deltaphi/RR32CanController/src/application/controller/MasterControl.cpp

#include <application/controller/MasterControl.h>
#include <cstring>

#include "RR32Can/RR32Can.h"

namespace application {
namespace controller {

void MasterControl::begin(application::controller::SettingsStorageCbk& settingsCbk,
                          application::controller::TurnoutMapStorageCbk& turnoutMapStorageCallback,
                          application::controller::ActionlistStorageCbk& actionListCallback) {
  systemState = RR32Can::SystemState::UNKNOWN;

  inputState.reset();

  displayModel.begin();
  enterIdle();

  locoControl.begin();
  locoList.begin();

  turnoutControl.begin(actionListCallback, turnoutMapStorageCallback);

  settingsMenu.begin(settingsCbk);
  turnoutMenu.begin(turnoutMapStorageCallback);
}

void MasterControl::loop() {
  // Always evaluate the STOP key with no SHIFT support
  loopStopKey();

  checkStateTransition();
  forwardLoop();

  updateDisplayLoop();

  turnoutControl.loop(inputState);
}

void MasterControl::checkStateTransition() {
  switch (uiMode) {
    case UIMode::IDLE:
    case UIMode::LOCOCONTROL:
    case UIMode::LOCOLIST:
    case UIMode::SETTINGS:
    case UIMode::TURNOUTMAPPING:
      break;
    case UIMode::LOCODOWNLOAD:
      // Switch to control when an engine was downloaded.
      if (locoControl.hasValidEngine()) {
        enterLocoControl();
      }
  }
}

void MasterControl::forwardLoop() {
  // Depending on mode, loop the associated control
  switch (uiMode) {
    case UIMode::IDLE:
      idleControl.loop(inputState, *this);
      break;
    case UIMode::LOCOCONTROL:
    case UIMode::LOCODOWNLOAD:
      locoControl.loop(inputState, *this);
      break;
    case UIMode::LOCOLIST:
      locoList.loop(inputState, *this);
      break;
    case UIMode::SETTINGS:
      settingsMenu.loop(inputState, *this);
      break;
    case UIMode::TURNOUTMAPPING:
      turnoutMenu.loop(inputState, *this, turnoutControl.getTurnoutMap(),
                       turnoutControl.getActionListModel().getDb());
  }
}

void MasterControl::enterIdle() {
  printf("MasterControl::enterIdle\n");
  uiMode = UIMode::IDLE;
  idleControl.updateDisplayOnce(displayModel);
}

void MasterControl::enterLocoControl() {
  printf("MasterControl::enterLocoControl\n");
  if (!locoControl.hasValidEngine()) {
    enterIdle();
  } else {
    displayModel.disableCursor();
    uiMode = UIMode::LOCOCONTROL;
    locoControl.enterLocoControl(inputState);
    locoControl.requestLocoData();
    locoControl.updateDisplayOnce(displayModel);
  }
}

void MasterControl::enterLocoList() {
  printf("MasterControl::enterLocoList\n");
  uiMode = UIMode::LOCOLIST;
  inputState.loadEncoderPosition(locoList.getCurrentItem());
  locoList.RequestDownloadAtCursor();
  displayModel.disableCursor();
  locoList.forceDisplayUpdate();
}

void MasterControl::enterLocoDownload() {
  printf("MasterControl::enterLocoDownload\n");
  uiMode = UIMode::LOCODOWNLOAD;

  // Copy selected engine from locoList to locoControl and start the download of
  // data
  const RR32Can::LocomotiveShortInfo* locoInfo = locoList.getSelectedEngine();
  if (locoInfo == nullptr) {
    // No engine was selected, go to IDLE
    enterIdle();
  } else {
    if (!locoControl.setLocoInfo(*locoInfo)) {
      // Previous Engine was reselected, go to another mode
      if (locoControl.hasValidEngine()) {
        enterLocoControl();
      } else {
        enterIdle();
      }
    } else {
      // An actual change was made. Update the UI.
      locoControl.updateDisplayOnce(displayModel);

      // Request the "lokomotive" data.
      locoControl.requestLocoFile();
    }
  }
}

void MasterControl::enterSettingsMenu() {
  printf("MasterControl::enterSettingsMenu\n");
  uiMode = UIMode::SETTINGS;
  inputState.loadEncoderPosition(settingsMenu.getCurrentItem());
  settingsMenu.forceDisplayUpdate();
}

void MasterControl::enterTurnoutMenu() {
  printf("MasterControl::enterTurnoutMenu\n");
  uiMode = UIMode::TURNOUTMAPPING;
  displayModel.disableCursor();
  turnoutMenu.forceDisplayUpdate();
}

void MasterControl::updateDisplayLoop() {
  switch (uiMode) {
    case UIMode::IDLE:
      // Was set during entering, nothing to do.
      break;
    case UIMode::LOCOLIST:
      // Handled by LOCOLIST itself
      locoList.updateDisplay(displayModel);
      break;
    case UIMode::LOCODOWNLOAD:
    case UIMode::LOCOCONTROL:
      break;
    case UIMode::SETTINGS:
      settingsMenu.updateDisplay(displayModel);
      break;
    case UIMode::TURNOUTMAPPING:
      turnoutMenu.updateDisplay(displayModel, turnoutControl.getTurnoutMap());
  }

  // Always update the non-text loco artifacts
  locoControl.updateDisplayLoop(displayModel);
}

void MasterControl::loopStopKey() {
  // Read the STOP button
  if (inputState.isStopRisingEdge()) {
    if (displayModel.getSystemOn()) {
      RR32Can::RR32Can.SendSystemStop();
    } else {
      RR32Can::RR32Can.SendSystemGo();
    }
  }
}

RR32Can::Locomotive* MasterControl::getLoco(RR32Can::Locomotive::Uid_t engineUid) {
  RR32Can::Locomotive& loco = locoControl.getLoco();
  if (!loco.isFullDetailsKnown()) {
    return nullptr;
  }
  if (loco.getUidMasked() != engineUid) {
    return nullptr;
  }

  return &loco;
}

void MasterControl::setLocoVelocity(RR32Can::Locomotive::Uid_t uid, RR32Can::Velocity_t velocity) {
  if (getLoco(uid) != 0) {
    locoControl.setReceivedVelocity(velocity, *this);
  }
}

void MasterControl::setLocoVelocity(RR32Can::Velocity_t velocity) {
  locoControl.setReceivedVelocity(velocity, *this);
}

}  // namespace controller
}  // namespace application
