deltaphi/RR32CanController/src/application/controller/LocoList.h

#ifndef __APPLICATION__CONTROLLER__LOCOLIST_H__
#define __APPLICATION__CONTROLLER__LOCOLIST_H__

#include <RR32Can/LocoListConsumer.h>
#include <RR32Can/Locomotive.h>
#include "application/controller/AbstractMenu.h"
#include "application/model/DisplayModel.h"
#include "application/model/InputState.h"

namespace application {
namespace controller {

class MasterControl;

/*
 * \brief Class LocoList
 */
class LocoList : public application::controller::AbstractMenu {
 public:
  void begin();
  void loop(application::model::InputState& inputState, MasterControl& masterControl) override;

  /// Callback when a menu item is selected.
  void advanceMenu(MenuItemIndex_t menuItem, MasterControl& masterControl) override;

  /// Callback when the menu is aborted (shift+encoder)
  void abortMenu(MasterControl& masterControl) override;

  const RR32Can::LocomotiveShortInfo* getSelectedEngine();

  void getMenuItems(MenuItems_t& menuItems) override;

  void notifyEncoderMoved(MenuItemIndex_t newItem) override;

  MenuItemIndex_t getTotalMenuLength() override { return browser.getNumEnginesKnownByMaster(); }

  void RequestDownloadAtCursor();

 private:
  RR32Can::LocoListConsumer browser;
};

}  // namespace controller
}  // namespace application

#endif  // __APPLICATION__CONTROLLER__LOCOLIST_H__
