deltaphi/RR32CanController/src/application/controller/SettingsMenu.h

#ifndef __APPLICATION__CONTROLLER__SETTINGSMENU_H__
#define __APPLICATION__CONTROLLER__SETTINGSMENU_H__

#include "application/controller/AbstractMenu.h"
#include "application/controller/SettingsStorageCbk.h"
#include "application/model/InputState.h"
#include "application/model/Settings.h"

namespace application {
namespace controller {

class MasterControl;

/*
 * \brief Class SettingsMenu
 */
class SettingsMenu : public application::controller::AbstractMenu {
 public:
  static constexpr const uint8_t kNumMenuEntries = 3;

  void begin(application::controller::SettingsStorageCbk& storageCbk);

  const application::model::Settings& getUserSettings() const { return settings; }

 protected:
  /// Callback when a menu item is selected.
  void advanceMenu(MenuItemIndex_t menuItem, MasterControl& masterControl) override;

  /// Callback when the menu is aborted (shift+encoder)
  void abortMenu(MasterControl& masterControl) override;

  /**
   * \brief Callback to retrive an array of menuitems.
   *
   * This is called fairly frequently, thus it should be implemented
   * efficiently.
   */
  void getMenuItems(MenuItems_t& menuItems) override;

  /**
   * \brief Callback to obtian the current known length of the menu.
   *
   * The length is not assumed to be constant for a given menu.
   */
  MenuItemIndex_t getTotalMenuLength() override;

 private:
  static const char* kTurnoutMapping;
  static const char* kUseCAN;
  static const char* kUseWifi;
  static const char* kActionListMapping;
  static const char* kWifiSettingsMapping;
  static const char* kConnectionSettingsMapping;

  static const char* kMenuEntries[kNumMenuEntries];

  application::model::Settings settings;
  application::controller::SettingsStorageCbk* storageCbk = nullptr;
};

}  // namespace controller
}  // namespace application

#endif  // __APPLICATION__CONTROLLER__SETTINGSMENU_H__
