deltaphi/RR32CanController/src/hal/UIAssets.h

#ifndef __HAL__UIASSETS_H__
#define __HAL__UIASSETS_H__

#include <Arduino.h>

namespace hal {

enum class RR32SymbolNames : char {
  ARROW_LEFT_EMPTY = 1,
  ARROW_LEFT_FILLED = 2,
  ARROW_RIGHT_EMPTY = 3,
  ARROW_RIGHT_FILLED = 4,
  WIFI = 5
};

// Font generated or edited with the glyphEditor
constexpr const uint8_t RR32Symbols_8[] PROGMEM = {
    0x08,  // Width: 8
    0x08,  // Height: 8
    0x01,  // First char: 1
    0x05,  // Number of chars: 5
    // Jump Table:
    0x00, 0x00, 0x08, 0x08,  // 1
    0x00, 0x08, 0x08, 0x08,  // 2
    0x00, 0x10, 0x07, 0x08,  // 3
    0x00, 0x17, 0x07, 0x08,  // 4
    0x00, 0x1E, 0x08, 0x08,  // 5
    // Font Data:
    0x00, 0x18, 0x24, 0x42, 0xE7, 0x24, 0x24, 0x3C,  // 1
    0x00, 0x18, 0x3C, 0x7E, 0xFF, 0x3C, 0x3C, 0x3C,  // 2
    0x3C, 0x24, 0x24, 0xE7, 0x42, 0x24, 0x18,        // 3
    0x3C, 0x3C, 0x3C, 0xFF, 0x7E, 0x3C, 0x18,        // 4
    0x0A, 0x25, 0x15, 0xD5, 0xD5, 0x15, 0x25, 0x0A,  // 5
};

// Font generated or edited with the glyphEditor
constexpr const uint8_t RR32Symbols_10[] PROGMEM = {
    0x0A,  // Width: 10
    0x0A,  // Height: 10
    0x01,  // First char: 1
    0x05,  // Number of chars: 5
    // Jump Table:
    0x00, 0x00, 0x13, 0x0A,  // 1
    0x00, 0x13, 0x13, 0x0A,  // 2
    0x00, 0x26, 0x13, 0x0A,  // 3
    0x00, 0x39, 0x13, 0x0A,  // 4
    0x00, 0x4C, 0x13, 0x0A,  // 5
    // Font Data:
    0x30, 0x00, 0x48, 0x00, 0x84, 0x00, 0x02, 0x01, 0x01, 0x02, 0x87, 0x03, 0x84, 0x00, 0x84, 0x00,
    0x84, 0x00, 0xFC,  // 1
    0x30, 0x00, 0x78, 0x00, 0xFC, 0x00, 0xFE, 0x01, 0xFF, 0x03, 0xFF, 0x03, 0xFC, 0x00, 0xFC, 0x00,
    0xFC, 0x00, 0xFC,  // 2
    0xFC, 0x00, 0x84, 0x00, 0x84, 0x00, 0x84, 0x00, 0x87, 0x03, 0x01, 0x02, 0x02, 0x01, 0x84, 0x00,
    0x48, 0x00, 0x30,  // 3
    0xFC, 0x00, 0xFC, 0x00, 0xFC, 0x00, 0xFC, 0x00, 0xFF, 0x03, 0xFF, 0x03, 0xFE, 0x01, 0xFC, 0x00,
    0x78, 0x00, 0x30,  // 4
    0x08, 0x00, 0x24, 0x00, 0x92, 0x00, 0x52, 0x00, 0x49, 0x03, 0x49, 0x03, 0x52, 0x00, 0x92, 0x00,
    0x24, 0x00, 0x08,  // 5
};

}  // namespace hal

#endif  // __HAL__UIASSETS_H__
