deltaphi/RR32CanController/src/controller/Input.h

#ifndef __CONTROLLER__INPUT_H__
#define __CONTROLLER__INPUT_H__

#include "AsyncShiftIn.h"

#include "application/model/InputState.h"

namespace controller {

/*
 * \brief Class Input.
 *
 * Reads the encoder and all buttons (shift register or otherwise)
 */
class Input {
 public:
  void begin();

  void loop() {
    loopEncoder();
    loopShiftRegister();
  }

  application::model::InputState& getInputState() { return inputState; }

  void shiftIn_reset(const AsyncShiftIn* shiftIn);
  void shiftIn_shift(const AsyncShiftIn* asyncShiftIn, unsigned int bitNumber,
                     uint8_t state);

 private:
  void loopEncoder();
  void loopShiftRegister();

  /**
   * \brief Variable stating whether the shift register has been initialized.
   */
  boolean initialized;

  /**
   * \brief The shift register.
   */
  AsyncShiftIn shiftRegister0;

  application::model::InputState inputState;
};

}  // namespace controller

#endif  // __CONTROLLER__INPUT_H__
