deltaphi/RR32CanController/src/RR32Can/Data.h

#ifndef __RR32Can__DATA_H__
#define __RR32Can__DATA_H__

#include <Arduino.h>

#include "RR32Can/constants.h"

namespace RR32Can {

/**
 * \brief Class to represent the payload of a Marklin CAN packet.
 *
 * This class represents the untyped payload and can be sent or received from
 * CAN.
 */
struct Data {
  constexpr static const uint8_t kDataBufferLength = CanDataMaxLength + 1;

  /// Data Length C... . actual calue ist 4 bit only.
  uint8_t dlc = 0;
  /// Actual data. An extra byte is prepared to allow for the use of snprintf.
  uint8_t data[kDataBufferLength] = {0, 0, 0, 0, 0, 0, 0, 0};

  /**
   * \brief Print the DLC and Data field as Hex values.
   */
  void printAsHex() const;

  /**
   * \brief Print the Payload as characters.
   */
  void printAsText() const;

  const char* dataAsString() const {
    const uint8_t* ptr = data;
    return reinterpret_cast<const char*>(ptr);
  }

  char* dataAsString() {
    uint8_t* ptr = data;
    return reinterpret_cast<char*>(ptr);
  }
};

} /* namespace RR32Can */

#endif
