deltaphi/RR32CanController/src/RR32Can/Data.cpp

#include "RR32Can/Data.h"

namespace RR32Can {

void Data::printAsHex() const {
  for (uint8_t i = 0; i < this->dlc; ++i) {
    Serial.print(" ");
    Serial.print(this->data[i], HEX);
  }
}

void Data::printAsText() const {
  for (uint8_t i = 0; i < this->dlc; ++i) {
    Serial.print(static_cast<char>(this->data[i]));
  }
}

} /* namespace RR32Can */
