deltaphi/RR32CanController/src/RR32Can/utils.cpp

#include "RR32Can/utils.h"

namespace RR32Can {

uint16_t computeSenderHash(uint32_t uid) {
  uid = ((uid >> 3) & 0xFFFFFF00) | (uid & 0x7F);
  uint16_t lowBytes = uid;
  uint16_t highBytes = (uid >> 16);
  return lowBytes ^ highBytes;
}

}  // namespace RR32Can
